mroukema/Explorer-Pi-Keyboard/files/thumb/right-thumb-top.stl

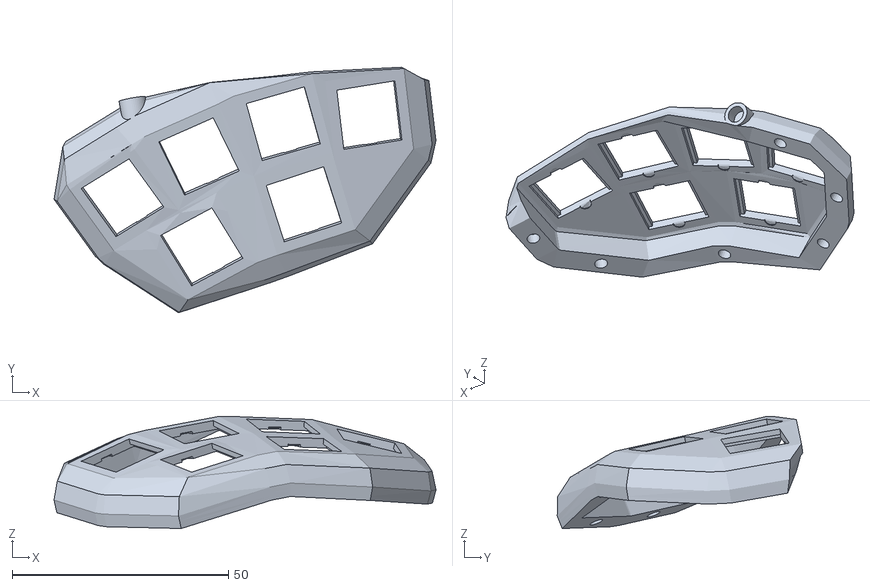
[picture p20: CAD file, 2023-10-31]
files/thumb/right-thumb-top.stl
88.4 x 56.8 x 25.9
