mroukema/Explorer-Pi-Keyboard/files/thumb/left-support-sturt-long.stl

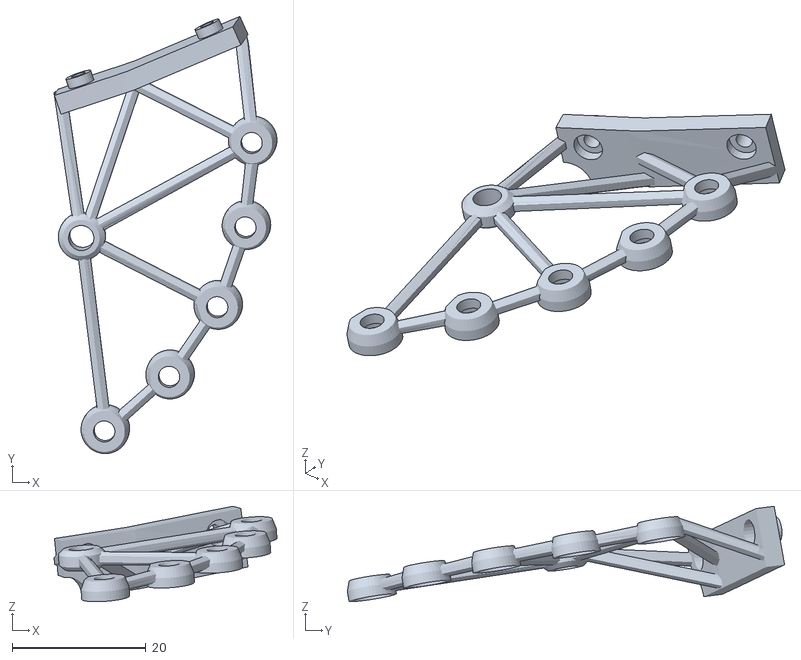
[picture p21: CAD file, 2023-10-31]
files/thumb/left-support-sturt-long.stl
33.4 x 65.5 x 14.3
