mroukema/Explorer-Pi-Keyboard/files/thumb/left-thumb-top.stl

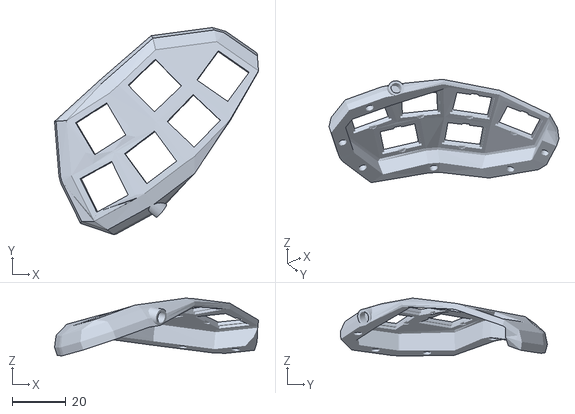
[picture p22: CAD file, 2023-10-31]
files/thumb/left-thumb-top.stl
75.7 x 76.8 x 21.5
